foldvarid93/JBC_SolderingStation/01_Version1/02_Software/03_Matlab/untitled.jpg

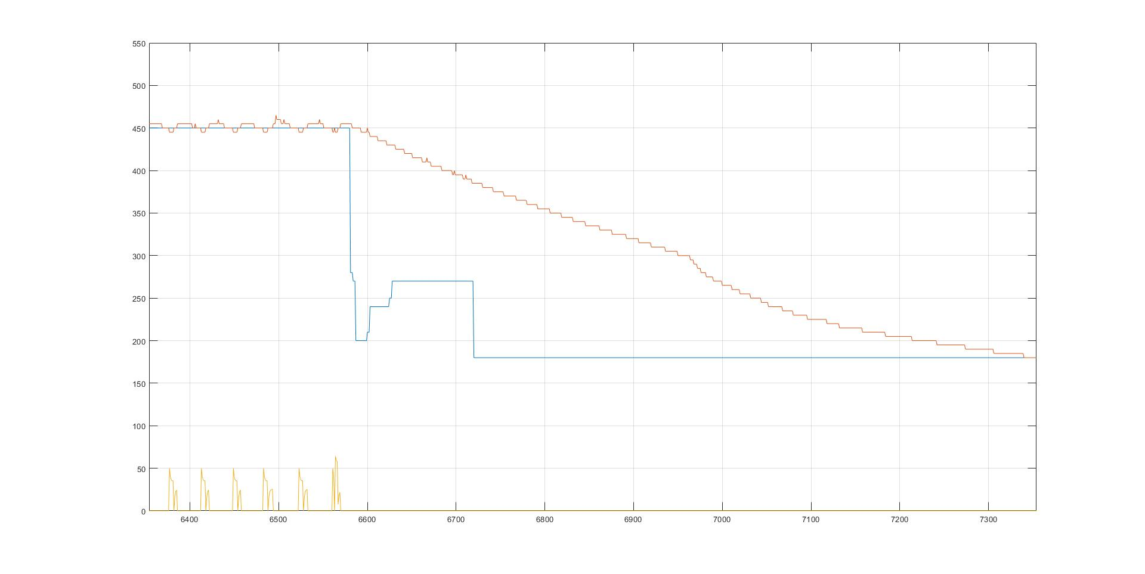
01_Version1/02_Software/03_Matlab/untitled.jpg
