foldvarid93/JBC_SolderingStation/01_Version1/02_Software/03_Matlab/WebinarElement14/3 Temperature Logging/TMP36_DataSheet_Image.JPG

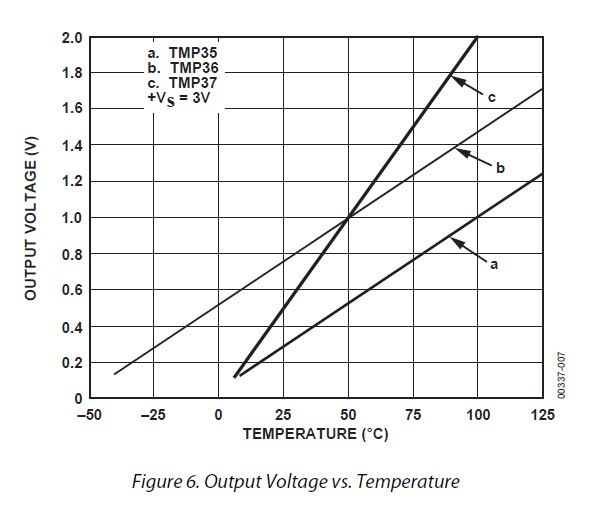
01_Version1/02_Software/03_Matlab/WebinarElement14/3 Temperature Logging/TMP36_DataSheet_Image.JPG
