foldvarid93/JBC_SolderingStation/01_Version1/01_Hardware/02_3D/Assem1.SLDASM

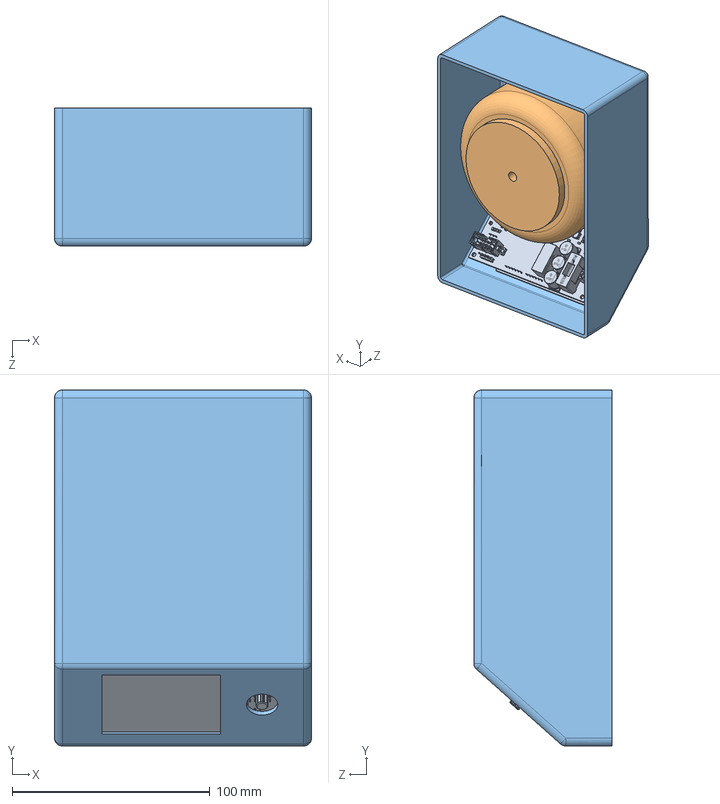
[picture p31: CAD file, 2023-04-08]
01_Version1/01_Hardware/02_3D/Assem1.SLDASM
130.0 x 180.0 x 70.0 mm
JBC_SolderingIron2
Transformer
housing
