foldvarid93/JBC_SolderingStation/01_Version1/01_Hardware/02_3D/JBC_SolderingIron.SLDASM

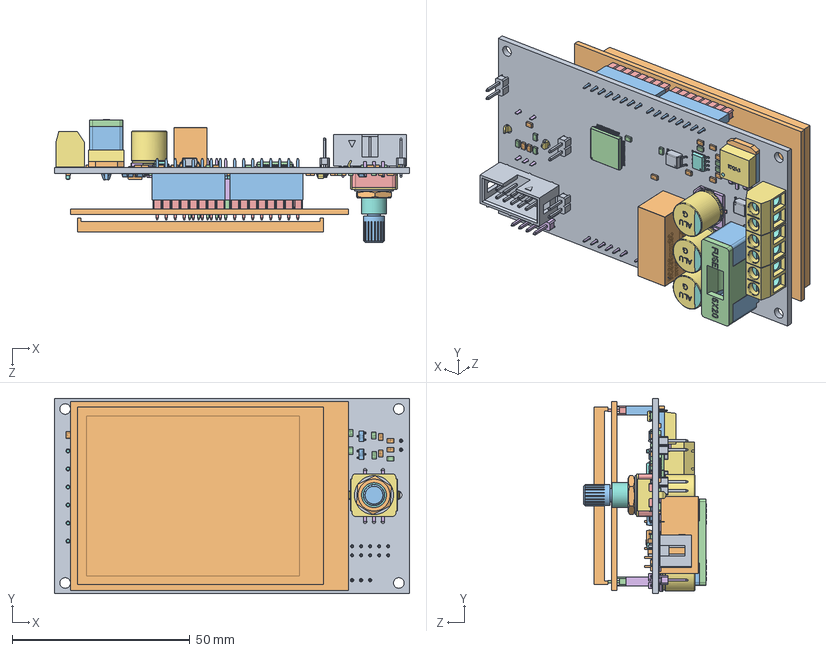
[picture p32: CAD file, 2023-04-08]
01_Version1/01_Hardware/02_3D/JBC_SolderingIron.SLDASM
100.0 x 55.0 x 34.7 mm
0805_Fekete_R x 35
SOT23 x 5
0805_Barna_C x 26
Pins_1 x 3
Fuss_1 x 3
K_X_F6rper_1 x 3
Beschriftung_1 x 3
SIL2 x 3
baseboard
HEADER8 x 2
SIL6 x 2
SIL8 x 2
HEADER6 x 2
User_Library-SOT23-6-2
SO-8 x 2
SO4-170-2.54 x 2
mps_dcdc_ncs3s_sc_a
User_Library-SOT-223-1
User_Library-LQFP64-0_5
SW3dPS-TO263-3S_Board9
SW3dPS-TO263-3S_Extruded14 x 2
SW3dPS-TO263-3S_Extruded11
SW3dPS-TO263-3S_Cylinder1
SW3dPS-TO263-3S_Extruded12
SW3dPS-TO263-3S_Extruded21
SW3dPS-TO263-3S_Extruded16
SW3dPS-TO263-3S_Extruded19
SW3dPS-TO263-3S_Board5 x 2
SW3dPS-TO263-3S_Extruded13 x 2
SW3dPS-TO263-3S_Extruded18
SW3dPS-TO263-3S_Board7
SW3dPS-TO263-3S_Board6
SW3dPS-TO263-3S_Extruded15
SW3dPS-TO263-3S_Extruded17
SW3dPS-TO263-3S_Board8
SW3dPS-TO263-3S_Extruded20
SIL4
User_Library-TB2_TB_case_1 x 3
User_Library-TB2_TB_screw_1 x 6
BH-10_64
1812L
12mm_Incremental_Encoder_Base_1
12mm_Incremental_Encoder_Pin_1 x 5
12mm_Incremental_Encoder_Anti-Rotation_Plate_1
12mm_Incremental_Encoder_Threaded_Tube_1
12mm_Incremental_Encoder_Washer_1
M7x0.75_Hex_Nut_1
12mm_Incremental_Encoder_Shaft
pin x 4
pin(Mirror) x 4
icbody x 4
User_Library-Tantalum_Capacitor_Case_A_Tantalum_case_A_part1 x 2
User_Library-Tantalum_Capacitor_Case_A_Tantalum_case_A_part2 x 4
SOIC-4_(Fairchild)
