foldvarid93/JBC_SolderingStation/01_Version1/01_Hardware/02_3D/v2/RPC1-12RB-6P.SLDPRT

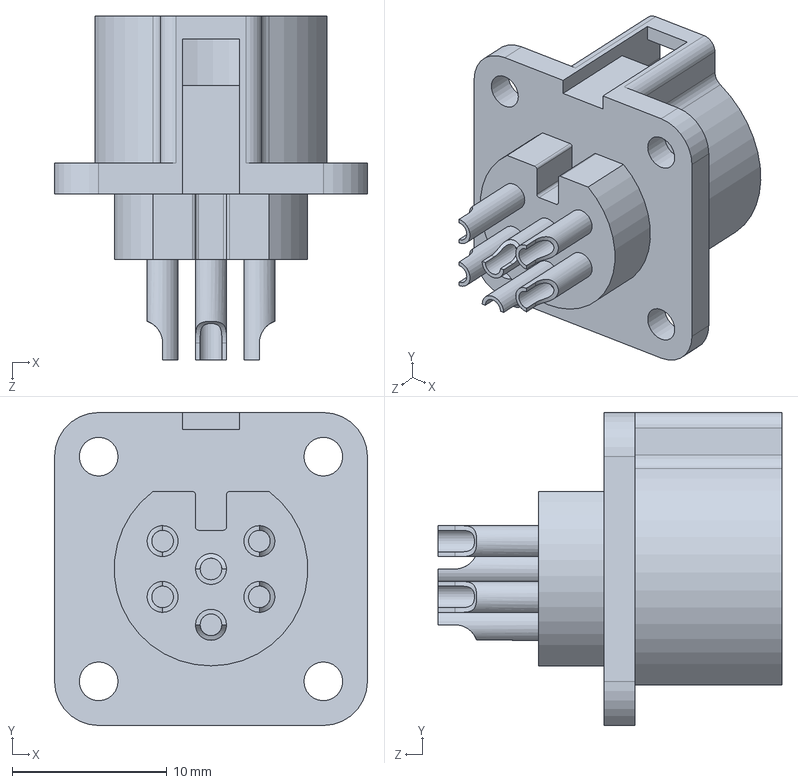
[picture p33: CAD file, 2023-04-08]
01_Version1/01_Hardware/02_3D/v2/RPC1-12RB-6P.SLDPRT
20.2 x 20.2 x 22.2 mm
