foldvarid93/JBC_SolderingStation/01_Version1/01_Hardware/02_3D/v2/PowerConn.SLDPRT

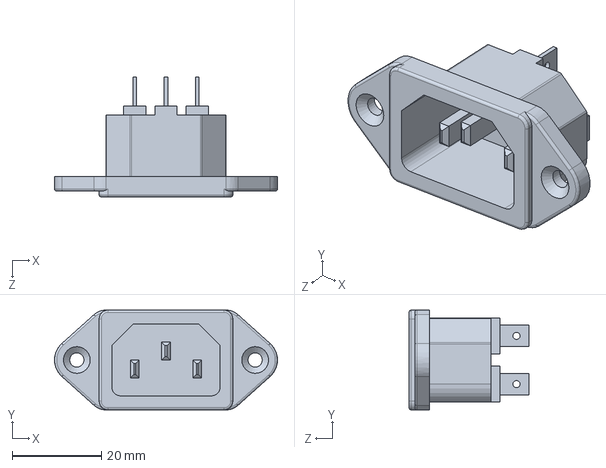
[picture p34: CAD file, 2023-04-08]
01_Version1/01_Hardware/02_3D/v2/PowerConn.SLDPRT
50.0 x 22.4 x 26.9 mm
