foldvarid93/JBC_SolderingStation/01_Version1/01_Hardware/02_3D/v2/haz1.SLDPRT

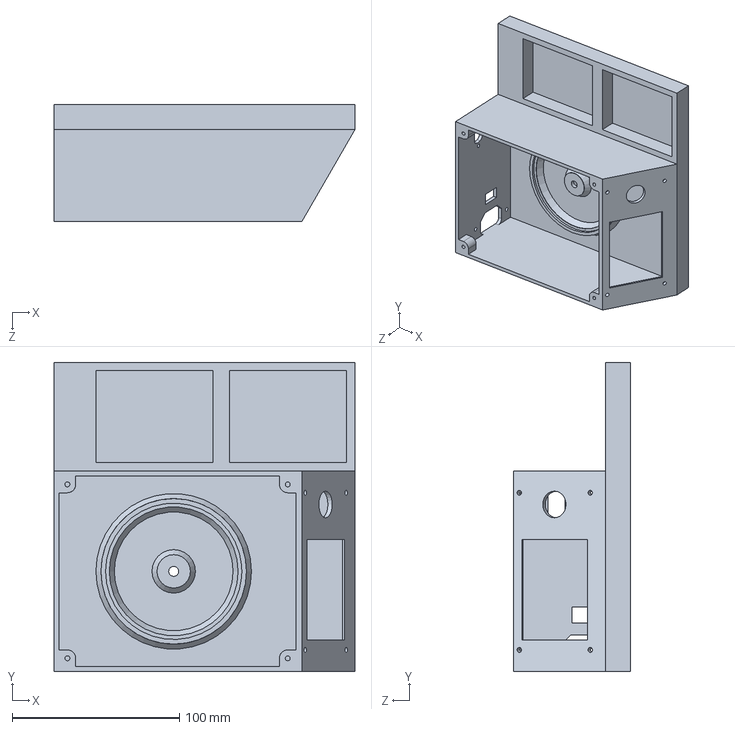
[picture p35: CAD file, 2023-04-08]
01_Version1/01_Hardware/02_3D/v2/haz1.SLDPRT
180.0 x 185.0 x 70.0 mm
