foldvarid93/JBC_SolderingStation/01_Version1/01_Hardware/02_3D/v2/D-Sub_9.STEP

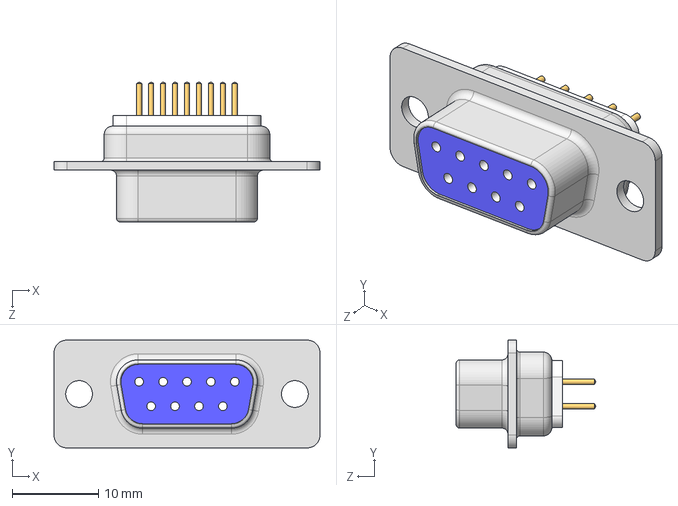
[picture p36: CAD file, 2023-04-08]
01_Version1/01_Hardware/02_3D/v2/D-Sub_9.STEP
30.8 x 12.5 x 16.2 mm
