foldvarid93/JBC_SolderingStation/01_Version1/01_Hardware/02_3D/v2/User Library-KCD11.step

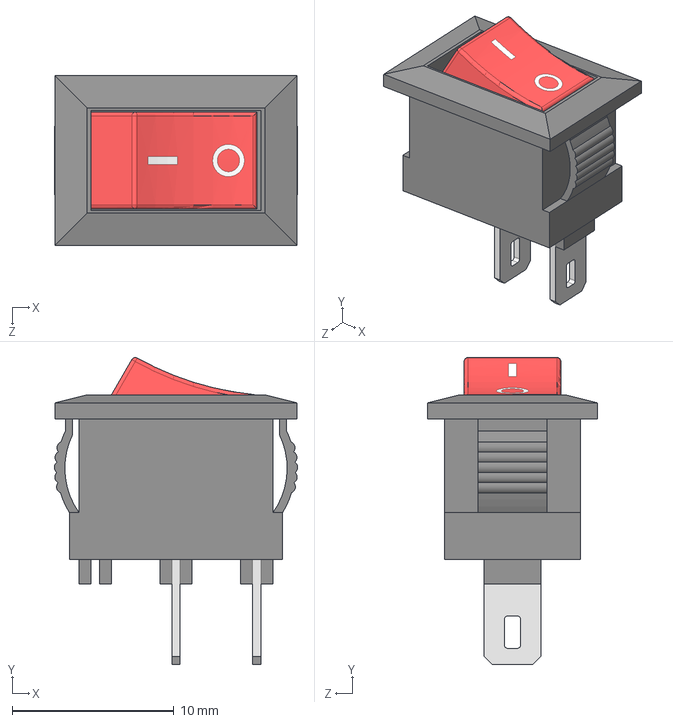
[picture p37: CAD file, 2023-04-08]
01_Version1/01_Hardware/02_3D/v2/User Library-KCD11.step
15.1 x 19.0 x 10.5 mm
