foldvarid93/JBC_SolderingStation/02_Version2/02_Software/01_EmbeddedSw/Application/inc/Application.h

/*
 * Application.h
 *
 *  Created on: Nov 1, 2019
 */

#ifndef APPLICATION_H_
#define APPLICATION_H_
/*includes*/
#include "main.h"
#include "tim.h"
#include "stdlib.h"
#include "string.h"
#include "stdio.h"
#include "math.h"
#include "adc.h"
#include "i2c.h"
#include "tim.h"
#include "usart.h"
#include "gpio.h"
#include "stdbool.h"
#include "eeprom.h"
#include "crc.h"
#include "DIALOG.h"
#include "GUI.h"
#include "portmacro.h"
/*Defines*/
#define NumberOfADCSampleAvegrage (3u)
/*Function declarations*/
void LCD_text(const char *q);
void LCD_write(unsigned char c, unsigned char d);
void LCD_init(void);
void user_pwm_setvalue(uint16_t value);
void ftoa(float n, char *res, int afterpoint);
void SendMeasurements(void);
void MainTask(void);
void MainInit(void);
void StateMachine(void);
extern void StateMachine(void);
void PID_Discrete(void);
void PID_Continous(void);
void InterruptTaskHandler(uint16_t);
void TimerCallback_1ms(void);
#endif /* APPLICATION_H_ */
