foldvarid93/JBC_SolderingStation/02_Version2/02_Software/01_EmbeddedSw/LCD/inc/ILI9341.h

/**
 * @file ILI9341.h
 *
 */

#ifndef ILI9341_H
#define ILI9341_H

#ifdef __cplusplus
extern "C" {
#endif

/*********************
 *      INCLUDES
 *********************/
#include <stdbool.h>
#include "LCDConf.h"
#ifndef LV_DRV_NO_CONF
#ifdef LV_CONF_INCLUDE_SIMPLE
#include "lv_drv_conf.h"
#else
#include "lv_drv_conf.h"
#endif
#endif

#if USE_ILI9341

#ifdef LV_LVGL_H_INCLUDE_SIMPLE
#include "lvgl.h"
#else
#include "../../../lvgl/lvgl.h"
#endif

#if LV_COLOR_DEPTH != 16
#error "ILI9341 currently supports 'LV_COLOR_DEPTH == 16'. Set it in lv_conf.h"
#endif

#if LV_COLOR_16_SWAP != 1
//#error "ILI9341 SPI requires LV_COLOR_16_SWAP == 1. Set it in lv_conf.h"
#endif

/*********************
 *      DEFINES
 *********************/
#define ILI9341_BGR true
#define ILI9341_RGB false

#define ILI9341_CMD_MODE    0
#define ILI9341_DATA_MODE   1

#define ILI9341_TFTWIDTH    240
#define ILI9341_TFTHEIGHT   320

/**********************
 *      TYPEDEFS
 **********************/

/**********************
 * GLOBAL PROTOTYPES
 **********************/
void ili9341_init(void);
void ili9341_flush(lv_disp_drv_t * drv, const lv_area_t * area, lv_color_t * color_p);
void ili9341_rotate(int degrees, bool bgr);
/**********************
 *      MACROS
 **********************/

#endif /* USE_ILI9341 */

#ifdef __cplusplus
} /* extern "C" */
#endif

#endif /* ILI9341_H */
