foldvarid93/JBC_SolderingStation/02_Version2/02_Software/01_EmbeddedSw/GUI/inc/GUIDRV_Lin_Private.h

#define GUIDRV_LIN_PRIVATE_H
#include <string.h>
#if defined(__cplusplus)
extern "C" {
#endif
#if defined(WIN32)
  U16  SIM_Lin_ReadMem16  (unsigned int Off);
  U32  SIM_Lin_ReadMem32  (unsigned int Off);
  U8   SIM_Lin_ReadMem08p (U8  * p);
  U32  SIM_Lin_ReadMem32p (U32 * p);
  void SIM_Lin_WriteMem16 (unsigned int Off, U16 Data);
  void SIM_Lin_WriteMem32 (unsigned int Off, U32 Data);
  void SIM_Lin_WriteMem08p(U8  * p, U8 Data);
  void SIM_Lin_WriteMem16p(U16 * p, U16 Data);
  void SIM_Lin_WriteMem32p(U32 * p, U32 Data);
  void SIM_Lin_memcpy     (void * pDst, const void * pSrc, int Len);
  void SIM_Lin_memset     (void * pDst, U8 Value, U32 Len);
  void SIM_Lin_SetVRAMAddr(int LayerIndex, void * pVRAM);
  void SIM_Lin_SetVRAMSize(int LayerIndex, int vxSize, int vySize, int xSize, int ySize);
  void SIM_Lin_CopyBuffer (int IndexSrc, int IndexDst);
  void SIM_Lin_ShowBuffer (int Index);
  #define LCD_READ_MEM16(VRAMAddr, Off)        SIM_Lin_ReadMem16(Off)
  #define LCD_READ_MEM32(VRAMAddr, Off)        SIM_Lin_ReadMem32(Off)
  #define LCD_READ_MEM08P(p)                   SIM_Lin_ReadMem08p(p)
  #define LCD_READ_MEM32P(p)                   SIM_Lin_ReadMem32p(p)
  #define LCD_WRITE_MEM16(VRAMAddr, Off, Data) SIM_Lin_WriteMem16(Off, Data)
  #define LCD_WRITE_MEM32(VRAMAddr, Off, Data) SIM_Lin_WriteMem32(Off, Data)
  #define LCD_WRITE_MEM08P(p, Data)            SIM_Lin_WriteMem08p(p, Data)
  #define LCD_WRITE_MEM16P(p, Data)            SIM_Lin_WriteMem16p(p, Data)
  #define LCD_WRITE_MEM32P(p, Data)            SIM_Lin_WriteMem32p(p, Data)
  #undef  GUI__MEMCPY
  #define GUI__MEMCPY(pDst, pSrc, Len)         SIM_Lin_memcpy(pDst, pSrc, Len)
  #undef  GUI__MEMSET
  #define GUI__MEMSET(pDst, Value, Len)        SIM_Lin_memset(pDst, Value, Len)
#else
  #define LCD_READ_MEM16(VRAMAddr, Off)        (*((U16 *)VRAMAddr + (U32)Off))
  #define LCD_READ_MEM32(VRAMAddr, Off)        (*((U32 *)VRAMAddr + (U32)Off))
  #define LCD_READ_MEM08P(p)                   (*((U8  *)p))
  #define LCD_READ_MEM32P(p)                   (*((U32 *)p))
  #define LCD_WRITE_MEM16(VRAMAddr, Off, Data) *((U16 *)VRAMAddr + (U32)Off) = (U16)(Data)
  #define LCD_WRITE_MEM32(VRAMAddr, Off, Data) *((U32 *)VRAMAddr + (U32)Off) = Data
  #define LCD_WRITE_MEM08P(p, Data)            *((U8  *)p) = (U8)(Data)
  #define LCD_WRITE_MEM16P(p, Data)            *((U16 *)p) = (U16)(Data)
  #define LCD_WRITE_MEM32P(p, Data)            *((U32 *)p) = Data
#endif
  #define WRITE_MEM16(VRAMAddr, Off, Data) LCD_WRITE_MEM16(VRAMAddr, Off, Data)
  #define WRITE_MEM32(VRAMAddr, Off, Data) LCD_WRITE_MEM32(VRAMAddr, Off, Data)
  #define READ_MEM08P(p)                   LCD_READ_MEM08P(p)
  #define READ_MEM16(VRAMAddr, Off)        LCD_READ_MEM16(VRAMAddr, Off)
  #define READ_MEM32(VRAMAddr, Off)        LCD_READ_MEM32(VRAMAddr, Off)
  #define READ_MEM32P(p)                   LCD_READ_MEM32P(p)
  #define WRITE_MEM08P(p, Data)            LCD_WRITE_MEM08P(p, Data)
  #define WRITE_MEM16P(p, Data)            LCD_WRITE_MEM16P(p, Data)
  #define WRITE_MEM32P(p, Data)            LCD_WRITE_MEM32P(p, Data)
#define OFF2PTR08(VRAMAddr, Off)     (U8  *)((U8 *)VRAMAddr + (Off     ))
#define OFF2PTR16(VRAMAddr, Off)     (U16 *)((U8 *)VRAMAddr + (Off << 1))
#define OFF2PTR32(VRAMAddr, Off)     (U32 *)((U8 *)VRAMAddr + (Off << 2))
#define DRIVER_CONTEXT DRIVER_CONTEXT_LIN
#define DEFAULT_CONTEXT_MEMBERS                               \
  U32 VRAMAddr;                                               \
  U32 BaseAddr;                                               \
  U32 * aBufferPTR;                                           \
  int BufferIndex;                                            \
  int xSize, ySize;                                           \
  int vxSize, vySize;                                         \
  int vxSizePhys;                                             \
  int xPos, yPos;                                             \
  int Alpha;                                                  \
  int IsVisible;                                              \
  void (* pfFillRect)  (int ,                 \
                        int ,                         \
                        int ,                         \
                        int ,                         \
                        int ,                         \
                        U32 );                \
  void (* pfCopyBuffer)(int ,                 \
                        int ,                   \
                        int );                  \
  void (* pfDrawBMP1)  (int ,                 \
                        int ,                          \
                        int ,                          \
                        U8 const * ,                   \
                        int ,                       \
                        int ,                      \
                        int ,                      \
                        int ,               \
                        const LCD_PIXELINDEX * ); \
  void (* pfDrawBMP8)  (int ,                 \
                        int ,                          \
                        int ,                          \
                        U8 const * ,                   \
                        int ,                      \
                        int ,                      \
                        int ,               \
                        const LCD_PIXELINDEX * ); \
  void (* pfCopyRect)  (int ,                 \
                        int ,                         \
                        int ,                         \
                        int ,                         \
                        int ,                         \
                        int ,                      \
                        int );                     \
  void (* pfSetPos)    (int ,                 \
                        int ,                       \
                        int );
  #define PRIVATE_CONTEXT_MEMBERS
#define DEFAULT_MANAGEMENT_GETDEVFUNC()                                             \
  case LCD_DEVFUNC_SET_VRAM_ADDR:                                                   \
    return (void (*)(void))_SetVRAMAddr;                                            \
  case LCD_DEVFUNC_SET_BUFFERPTR:                                                   \
    return (void (*)(void))_SetVRAM_BufferPTR;                                      \
  case LCD_DEVFUNC_SET_VSIZE:                                                       \
    return (void (*)(void))_SetVSize;                                               \
  case LCD_DEVFUNC_SET_SIZE:                                                        \
    return (void (*)(void))_SetSize;                                                \
  case LCD_DEVFUNC_SETPOS:                                                          \
    return (void (*)(void))_SetPos;                                                 \
  case LCD_DEVFUNC_GETPOS:                                                          \
    return (void (*)(void))_GetPos;                                                 \
  case LCD_DEVFUNC_SETALPHA:                                                        \
    return (void (*)(void))_SetAlpha;                                               \
  case LCD_DEVFUNC_SETVIS:                                                          \
    return (void (*)(void))_SetVis;                                                 \
  case LCD_DEVFUNC_INIT:                                                            \
    return (void (*)(void))_Init;                                                   \
  case LCD_DEVFUNC_ON:                                                              \
    return (void (*)(void))_On;                                                     \
  case LCD_DEVFUNC_OFF:                                                             \
    return (void (*)(void))_Off;                                                    \
  case LCD_DEVFUNC_ALPHAMODE:                                                       \
    return (void (*)(void))_SetAlphaMode;                                           \
  case LCD_DEVFUNC_CHROMAMODE:                                                      \
    return (void (*)(void))_SetChromaMode;                                          \
  case LCD_DEVFUNC_CHROMA:                                                          \
    return (void (*)(void))_SetChroma;                                              \
  case LCD_DEVFUNC_COPYBUFFER:                                                      \
    return (void (*)(void))_CopyBuffer;                                             \
  case LCD_DEVFUNC_SHOWBUFFER:                                                      \
    return (void (*)(void))_ShowBuffer;                                             \
  case LCD_DEVFUNC_SETFUNC:                                                         \
    return (void (*)(void))_SetDevFunc;                                             \
  case LCD_DEVFUNC_FILLRECT:                                                        \
    return (void (*)(void))((DRIVER_CONTEXT *)(*ppDevice)->u.pContext)->pfFillRect; \
  case LCD_DEVFUNC_DRAWBMP_1BPP:                                                    \
    return (void (*)(void))((DRIVER_CONTEXT *)(*ppDevice)->u.pContext)->pfDrawBMP1; \
  case LCD_DEVFUNC_DRAWBMP_8BPP:                                                    \
    return (void (*)(void))((DRIVER_CONTEXT *)(*ppDevice)->u.pContext)->pfDrawBMP8; \
  case LCD_DEVFUNC_COPYRECT:                                                        \
    return (void (*)(void))((DRIVER_CONTEXT *)(*ppDevice)->u.pContext)->pfCopyRect;
  #define PRIVATE_MANAGEMENT_GETDEVFUNC()
#define DEFAULT_MANAGEMENT_SETDEVFUNC()                                                                                                                                      \
    case LCD_DEVFUNC_FILLRECT:                                                                                                                                               \
      pContext->pfFillRect   = (void (*)(int LayerIndex, int x0, int y0, int x1, int y1, U32 PixelIndex))pFunc;                                                              \
      break;                                                                                                                                                                 \
    case LCD_DEVFUNC_COPYBUFFER:                                                                                                                                             \
      pContext->pfCopyBuffer = (void (*)(int LayerIndex, int IndexSrc, int IndexDst))pFunc;                                                                                  \
      break;                                                                                                                                                                 \
    case LCD_DEVFUNC_DRAWBMP_1BPP:                                                                                                                                           \
      pContext->pfDrawBMP1   = (void (*)(int LayerIndex, int x, int y, U8 const * p, int Diff, int xSize, int ySize, int BytesPerLine, const LCD_PIXELINDEX * pTrans))pFunc; \
      break;                                                                                                                                                                 \
    case LCD_DEVFUNC_DRAWBMP_8BPP:                                                                                                                                           \
      pContext->pfDrawBMP8   = (void (*)(int LayerIndex, int x, int y, U8 const * p, int xSize, int ySize, int BytesPerLine, const LCD_PIXELINDEX * pTrans))pFunc;           \
      break;                                                                                                                                                                 \
    case LCD_DEVFUNC_COPYRECT:                                                                                                                                               \
      pContext->pfCopyRect   = (void (*)(int LayerIndex, int x0, int y0, int x1, int y1, int xSize, int ySize))pFunc;                                                        \
      break;                                                                                                                                                                 \
    case LCD_DEVFUNC_SETPOS:                                                                                                                                                 \
      pContext->pfSetPos     = (void (*)(int LayerIndex, int xPos, int yPos))pFunc;                                                                                          \
      break;
  #define PRIVATE_MANAGEMENT_SETDEVFUNC()
  #define LCD_MIRROR 0
#if (LCD_MIRROR == 2)
#define MIRROR(x) x = ((x & 0x000000ffUL) <<  8) \
                    | ((x & 0x0000ff00UL) >>  8) \
                    | ((x & 0x00ff0000UL) <<  8) \
                    | ((x & 0xff000000UL) >>  8)
#else
#define MIRROR(x) x = ((x & 0x000000ffUL) << 24) \
                    | ((x & 0x0000ff00UL) <<  8) \
                    | ((x & 0x00ff0000UL) >>  8) \
                    | ((x & 0xff000000UL) >> 24)
#endif
typedef struct {
  DEFAULT_CONTEXT_MEMBERS
  PRIVATE_CONTEXT_MEMBERS
} DRIVER_CONTEXT;
static int _InitOnce(GUI_DEVICE * pDevice) {
  if (pDevice->u.pContext == NULL) {
    pDevice->u.pContext = GUI_ALLOC_GetFixedBlock(sizeof(DRIVER_CONTEXT));
    GUI__memset((U8 *)pDevice->u.pContext, 0, sizeof(DRIVER_CONTEXT));
  }
  return pDevice->u.pContext ? 0 : 1;
}
static void _GetRect(GUI_DEVICE * pDevice, LCD_RECT * pRect) {
  DRIVER_CONTEXT * pContext;
  pContext = (DRIVER_CONTEXT *)pDevice->u.pContext;
  pRect->x0 = 0;
  pRect->y0 = 0;
  pRect->x1 = pContext->vxSize - 1;
  pRect->y1 = pContext->vySize - 1;
}
static void _SetVis(GUI_DEVICE * pDevice, int OnOff) {
  DRIVER_CONTEXT * pContext;
  LCD_X_SETVIS_INFO Data = {0};
  _InitOnce(pDevice);
  if (pDevice->u.pContext) {
    pContext = (DRIVER_CONTEXT *)pDevice->u.pContext;
    pContext->IsVisible = OnOff;
    Data.OnOff = OnOff;
    LCD_X_DisplayDriver(pDevice->LayerIndex, LCD_X_SETVIS, (void *)&Data);
  }
}
static void _SetPos(GUI_DEVICE * pDevice, int xPos, int yPos) {
  DRIVER_CONTEXT * pContext;
  int xSizeDisplay, ySizeDisplay, xSizeLayer, ySizeLayer, BitsPerPixel;
  LCD_X_SETPOS_INFO PosInfo = {0};
  _InitOnce(pDevice);
  if (pDevice->u.pContext) {
    pContext = (DRIVER_CONTEXT *)pDevice->u.pContext;
    if (pContext->pfSetPos) {
      pContext->pfSetPos(pDevice->LayerIndex, xPos, yPos);
    } else {
      pContext->xPos = xPos;
      pContext->yPos = yPos;
      xSizeDisplay  = LCD_GetXSizeDisplay();
      ySizeDisplay  = LCD_GetYSizeDisplay();
      xSizeLayer    = pContext->xSize;
      ySizeLayer    = pContext->ySize;
      BitsPerPixel  = pDevice->pDeviceAPI->pfGetDevProp(pDevice, LCD_DEVCAP_BITSPERPIXEL);
      PosInfo.BytesPerPixel = (BitsPerPixel + 7) / 8;
      if (xPos < 0) {
        PosInfo.Off -= xPos * PosInfo.BytesPerPixel;
        PosInfo.xPos = 0;
        PosInfo.xLen = xSizeLayer + xPos;
      } else {
        PosInfo.xPos = xPos;
        PosInfo.xLen = xSizeLayer;
        if ((PosInfo.xPos + PosInfo.xLen) > xSizeDisplay) {
          PosInfo.xLen = xSizeDisplay - xPos;
        }
      }
      if (yPos < 0) {
        PosInfo.Off -= yPos * PosInfo.BytesPerPixel * xSizeLayer;
        PosInfo.yPos = 0;
        PosInfo.yLen = ySizeLayer + yPos;
      } else {
        PosInfo.yPos = yPos;
        PosInfo.yLen = ySizeLayer;
        if ((PosInfo.yPos + PosInfo.yLen) > ySizeDisplay) {
          PosInfo.yLen = ySizeDisplay - yPos;
        }
      }
      if ((PosInfo.xLen <= 0) || (PosInfo.yLen <= 0) || (PosInfo.xPos >= xSizeDisplay) || (PosInfo.yPos >= ySizeDisplay)) {
        if (pContext->IsVisible == 1) {
          _SetVis(pDevice, 0);
        }
        return;
      }
      if (pContext->IsVisible == 0) {
        _SetVis(pDevice, 1);
      }
      LCD_X_DisplayDriver(pDevice->LayerIndex, LCD_X_SETPOS, (void *)&PosInfo);
    }
  }
}
static void _GetPos(GUI_DEVICE * pDevice, int * pxPos, int * pyPos) {
  DRIVER_CONTEXT * pContext;
  _InitOnce(pDevice);
  if (pDevice->u.pContext) {
    pContext = (DRIVER_CONTEXT *)pDevice->u.pContext;
    *pxPos = pContext->xPos;
    *pyPos = pContext->yPos;
  }
}
static void _SetAlpha(GUI_DEVICE * pDevice, int Alpha) {
  DRIVER_CONTEXT * pContext;
  LCD_X_SETALPHA_INFO Data = {0};
  _InitOnce(pDevice);
  if (pDevice->u.pContext) {
    pContext = (DRIVER_CONTEXT *)pDevice->u.pContext;
    pContext->Alpha = Alpha;
    Data.Alpha = Alpha;
    LCD_X_DisplayDriver(pDevice->LayerIndex, LCD_X_SETALPHA, (void *)&Data);
  }
}
static int  _Init(GUI_DEVICE * pDevice) {
  int r;
  r = _InitOnce(pDevice);
  r |= LCD_X_DisplayDriver(pDevice->LayerIndex, LCD_X_INITCONTROLLER, NULL);
  return r;
}
static void _On (GUI_DEVICE * pDevice) {
  LCD_X_DisplayDriver(pDevice->LayerIndex, LCD_X_ON, NULL);
}
static void _Off (GUI_DEVICE * pDevice) {
  LCD_X_DisplayDriver(pDevice->LayerIndex, LCD_X_OFF, NULL);
}
static void _SetAlphaMode(GUI_DEVICE * pDevice, int AlphaMode) {
  LCD_X_SETALPHAMODE_INFO Data = {0};
  Data.AlphaMode = AlphaMode;
  LCD_X_DisplayDriver(pDevice->LayerIndex, LCD_X_SETALPHAMODE, (void *)&Data);
}
static void _SetChromaMode(GUI_DEVICE * pDevice, int ChromaMode) {
  LCD_X_SETCHROMAMODE_INFO Data = {0};
  Data.ChromaMode = ChromaMode;
  LCD_X_DisplayDriver(pDevice->LayerIndex, LCD_X_SETCHROMAMODE, (void *)&Data);
}
static void _SetChroma(GUI_DEVICE * pDevice, LCD_COLOR ChromaMin, LCD_COLOR ChromaMax) {
  LCD_X_SETCHROMA_INFO Data = {0};
  Data.ChromaMin = ChromaMin;
  Data.ChromaMax = ChromaMax;
  LCD_X_DisplayDriver(pDevice->LayerIndex, LCD_X_SETCHROMA, (void *)&Data);
}
static void _CopyBuffer(GUI_DEVICE * pDevice, int IndexSrc, int IndexDst) {
  DRIVER_CONTEXT * pContext;
  #if (!defined(WIN32))
    U32 AddrSrc, AddrDst;
    I32 BufferSize;
    int BitsPerPixel;
  #endif
  _InitOnce(pDevice);
  if (pDevice->u.pContext) {
    pContext = (DRIVER_CONTEXT *)pDevice->u.pContext;
    if (IndexSrc != IndexDst) {
      #if defined(WIN32)
        SIM_Lin_CopyBuffer(IndexSrc, IndexDst);
      #else
        BitsPerPixel = pDevice->pDeviceAPI->pfGetDevProp(pDevice, LCD_DEVCAP_BITSPERPIXEL);
        BufferSize = (((U32)pContext->vxSize * pContext->ySize * BitsPerPixel) >> 3);
        if (pContext->aBufferPTR) {
          AddrSrc = *(pContext->aBufferPTR + IndexSrc);
          AddrDst = *(pContext->aBufferPTR + IndexDst);
        } else {
          AddrSrc = pContext->BaseAddr + BufferSize * IndexSrc;
          AddrDst = pContext->BaseAddr + BufferSize * IndexDst;
        }
        if (pContext->pfCopyBuffer) {
          pContext->pfCopyBuffer(pDevice->LayerIndex, IndexSrc, IndexDst);
        } else {
          GUI__MEMCPY((void *)AddrDst, (void *)AddrSrc, BufferSize);
        }
        pContext->VRAMAddr = AddrDst;
      #endif
    }
  }
}
static void _ShowBuffer(GUI_DEVICE * pDevice, int Index) {
  LCD_X_SHOWBUFFER_INFO Data = {0};
  _InitOnce(pDevice);
  if (pDevice->u.pContext) {
    #if defined(WIN32)
      SIM_Lin_ShowBuffer(Index);
    #else
      Data.Index = Index;
      LCD_X_DisplayDriver(pDevice->LayerIndex, LCD_X_SHOWBUFFER, (void *)&Data);
    #endif
  }
}
static void _SetOrg(GUI_DEVICE * pDevice, int x, int y) {
  #if (!defined(WIN32))
    DRIVER_CONTEXT * pContext;
    int Orientation;
  #endif
  LCD_X_SETORG_INFO Data = {0};
  #if defined(WIN32)
    LCDSIM_SetOrg(x, y, pDevice->LayerIndex);
  #else
    pContext = (DRIVER_CONTEXT *)pDevice->u.pContext;
    Orientation  = LCD_GetMirrorXEx(pDevice->LayerIndex) * GUI_MIRROR_X;
    Orientation |= LCD_GetMirrorYEx(pDevice->LayerIndex) * GUI_MIRROR_Y;
    Orientation |= LCD_GetSwapXYEx (pDevice->LayerIndex) * GUI_SWAP_XY;
    switch (Orientation) {
    case 0:
      Data.xPos = x;
      Data.yPos = y;
      break;
    case GUI_MIRROR_X:
      Data.xPos = pContext->vxSize - pContext->xSize - x;
      Data.yPos = y;
      break;
    case GUI_MIRROR_Y:
      Data.xPos = x;
      Data.yPos = pContext->vySize - pContext->ySize - y;
      break;
    case GUI_MIRROR_X | GUI_MIRROR_Y:
      Data.xPos = pContext->vxSize - pContext->xSize - x;
      Data.yPos = pContext->vySize - pContext->ySize - y;
      break;
    case GUI_SWAP_XY:
      Data.xPos = y;
      Data.yPos = x;
      break;
    case GUI_SWAP_XY | GUI_MIRROR_X:
      Data.xPos = pContext->vySize - pContext->ySize  - y;
      Data.yPos = x;
      break;
    case GUI_SWAP_XY | GUI_MIRROR_Y:
      Data.xPos = y;
      Data.yPos = pContext->vxSize - pContext->xSize  - x;
      break;
    case GUI_SWAP_XY | GUI_MIRROR_X | GUI_MIRROR_Y:
      Data.xPos = pContext->vySize - pContext->ySize  - y;
      Data.yPos = pContext->vxSize - pContext->xSize  - x;
      break;
    }
    LCD_X_DisplayDriver(pDevice->LayerIndex, LCD_X_SETORG, (void *)&Data);
  #endif
}
static void _SetVRAMAddr(GUI_DEVICE * pDevice, void * pVRAM) {
  DRIVER_CONTEXT * pContext;
  LCD_X_SETVRAMADDR_INFO Data = {0};
  _InitOnce(pDevice);
  if (pDevice->u.pContext) {
    pContext = (DRIVER_CONTEXT *)pDevice->u.pContext;
    pContext->VRAMAddr = pContext->BaseAddr = (U32)pVRAM;
    Data.pVRAM = pVRAM;
    LCD_X_DisplayDriver(pDevice->LayerIndex, LCD_X_SETVRAMADDR, (void *)&Data);
  }
  #if defined(WIN32)
    SIM_Lin_SetVRAMAddr(pDevice->LayerIndex, pVRAM);
  #endif
}
static void _SetVRAM_BufferPTR(GUI_DEVICE * pDevice, U32 * pBufferPTR) {
  DRIVER_CONTEXT * pContext;
  _InitOnce(pDevice);
  if (pDevice->u.pContext) {
    pContext = (DRIVER_CONTEXT *)pDevice->u.pContext;
    pContext->aBufferPTR = pBufferPTR;
    pContext->VRAMAddr = *(pBufferPTR + 0);
  }
}
static void _SetVSize(GUI_DEVICE * pDevice, int xSize, int ySize) {
  DRIVER_CONTEXT * pContext;
  #if defined(WIN32)
    int NumBuffers;
  #endif
  _InitOnce(pDevice);
  if (pDevice->u.pContext) {
    #if defined(WIN32)
      NumBuffers = GUI_MULTIBUF_GetNumBuffers();
    #endif
    pContext = (DRIVER_CONTEXT *)pDevice->u.pContext;
    if (LCD_GetSwapXYEx(pDevice->LayerIndex)) {
      #if defined(WIN32)
        pContext->vxSize = xSize * NumBuffers;
      #else
        pContext->vxSize = xSize;
      #endif
      pContext->vySize = ySize;
      pContext->vxSizePhys = ySize;
    } else {
      pContext->vxSize = xSize;
      #if defined(WIN32)
        pContext->vySize = ySize * NumBuffers;
      #else
        pContext->vySize = ySize;
      #endif
      pContext->vxSizePhys = xSize;
    }
  }
  #if defined(WIN32)
    SIM_Lin_SetVRAMSize(pDevice->LayerIndex, pContext->vxSize, pContext->vySize, pContext->xSize, pContext->ySize);
  #endif
}
static void _SetSize(GUI_DEVICE * pDevice, int xSize, int ySize) {
  DRIVER_CONTEXT * pContext;
  LCD_X_SETSIZE_INFO Data = {0};
  _InitOnce(pDevice);
  if (pDevice->u.pContext) {
    pContext = (DRIVER_CONTEXT *)pDevice->u.pContext;
    if (pContext->vxSizePhys == 0) {
      if (LCD_GetSwapXYEx(pDevice->LayerIndex)) {
        pContext->vxSizePhys = ySize;
      } else {
        pContext->vxSizePhys = xSize;
      }
    }
    pContext->xSize = xSize;
    pContext->ySize = ySize;
    Data.xSize = xSize;
    Data.ySize = ySize;
    LCD_X_DisplayDriver(pDevice->LayerIndex, LCD_X_SETSIZE, (void *)&Data);
  }
}
#if defined(__cplusplus)
}
#endif
