foldvarid93/JBC_SolderingStation/02_Version2/02_Software/01_EmbeddedSw/GUI/inc/LISTWHEEL.h

/*********************************************************************
*                SEGGER Microcontroller GmbH & Co. KG                *
*        Solutions for real time microcontroller applications        *
**********************************************************************
*                                                                    *
*        (c) 1996 - 2017  SEGGER Microcontroller GmbH & Co. KG       *
*                                                                    *
*        Internet: www.segger.com    Support:  support@segger.com    *
*                                                                    *
**********************************************************************

** emWin V5.44 - Graphical user interface for embedded applications **
All  Intellectual Property rights  in the Software belongs to  SEGGER.
emWin is protected by  international copyright laws.  Knowledge of the
source code may not be used to write a similar product.  This file may
only be used in accordance with the following terms:

The  software has  been licensed  to STMicroelectronics International
N.V. a Dutch company with a Swiss branch and its headquarters in Plan-
les-Ouates, Geneva, 39 Chemin du Champ des Filles, Switzerland for the
purposes of creating libraries for ARM Cortex-M-based 32-bit microcon_
troller products commercialized by Licensee only, sublicensed and dis_
tributed under the terms and conditions of the End User License Agree_
ment supplied by STMicroelectronics International N.V.
Full source code is available at: www.segger.com

We appreciate your understanding and fairness.
----------------------------------------------------------------------

  ******************************************************************************
  * @attention
  *
  * <h2><center>&copy; Copyright (c) 2018 STMicroelectronics. 
  * All rights reserved.</center></h2>
  *
  * This software component is licensed by ST under Ultimate Liberty license SLA0044,
  * the "License"; You may not use this file except in compliance with the License.
  * You may obtain a copy of the License at:
  *                      http://www.st.com/SLA0044
  *
  ******************************************************************************
----------------------------------------------------------------------
File        : LISTWHEEL.h
Purpose     : LISTWHEEL widget include
--------------------END-OF-HEADER-------------------------------------
*/

#ifndef LISTWHEEL_H
#define LISTWHEEL_H

#include "WM.h"
#include "DIALOG_Intern.h"
#include "WIDGET.h"

#if GUI_WINSUPPORT

#if defined(__cplusplus)
  extern "C" {        // Make sure we have C-declarations in C++ programs
#endif

/*********************************************************************
*
*       Defines
*
**********************************************************************
*/
#define LISTWHEEL_CI_UNSEL 0
#define LISTWHEEL_CI_SEL   1

/*********************************************************************
*
*       Types
*
**********************************************************************
*/
typedef WM_HMEM LISTWHEEL_Handle;

/*********************************************************************
*
*       Standard member functions
*
**********************************************************************
*/
/*********************************************************************
*
*       Create functions
*
**********************************************************************
*/
LISTWHEEL_Handle LISTWHEEL_Create        (const GUI_ConstString * ppText, int x0, int y0, int xSize, int ySize, int Flags);
LISTWHEEL_Handle LISTWHEEL_CreateAsChild (const GUI_ConstString * ppText, WM_HWIN hWinParent, int x0, int y0, int xSize, int ySize, int Flags);
LISTWHEEL_Handle LISTWHEEL_CreateIndirect(const GUI_WIDGET_CREATE_INFO * pCreateInfo, WM_HWIN hWinParent, int x0, int y0, WM_CALLBACK * cb);
LISTWHEEL_Handle LISTWHEEL_CreateEx      (int x0, int y0, int xSize, int ySize, WM_HWIN hParent,
                                          int WinFlags, int ExFlags, int Id, const GUI_ConstString * ppText);
LISTWHEEL_Handle LISTWHEEL_CreateUser    (int x0, int y0, int xSize, int ySize, WM_HWIN hParent,
                                          int WinFlags, int ExFlags, int Id, const GUI_ConstString * ppText, int NumExtraBytes);

/*********************************************************************
*
*       The callback ...
*
* Do not call it directly ! It is only to be used from within an
* overwritten callback.
*/
void LISTWHEEL_Callback(WM_MESSAGE * pMsg);

/*********************************************************************
*
*       Member functions
*
**********************************************************************
*/
void      LISTWHEEL_AddString      (LISTWHEEL_Handle hObj, const char * s);
GUI_COLOR LISTWHEEL_GetBkColor     (LISTWHEEL_Handle hObj, unsigned int Index);
void *    LISTWHEEL_GetItemData    (LISTWHEEL_Handle hObj, unsigned Index); /* not to be documented */
void      LISTWHEEL_GetItemText    (LISTWHEEL_Handle hObj, unsigned Index, char * pBuffer, int MaxSize);
int       LISTWHEEL_GetItemFromPos (LISTWHEEL_Handle hObj, int yPos);
int       LISTWHEEL_GetLBorder     (LISTWHEEL_Handle hObj);
unsigned  LISTWHEEL_GetLineHeight  (LISTWHEEL_Handle hObj);
int       LISTWHEEL_GetNumItems    (LISTWHEEL_Handle hObj);
int       LISTWHEEL_GetPos         (LISTWHEEL_Handle hObj);
int       LISTWHEEL_GetRBorder     (LISTWHEEL_Handle hObj);
int       LISTWHEEL_GetSel         (LISTWHEEL_Handle hObj);
int       LISTWHEEL_GetSnapPosition(LISTWHEEL_Handle hObj);
int       LISTWHEEL_GetTextAlign   (LISTWHEEL_Handle hObj);
GUI_COLOR LISTWHEEL_GetTextColor   (LISTWHEEL_Handle hObj, unsigned int Index);
int       LISTWHEEL_GetUserData    (LISTWHEEL_Handle hObj, void * pDest, int NumBytes);
int       LISTWHEEL_IsMoving       (LISTWHEEL_Handle hObj);
void      LISTWHEEL_MoveToPos      (LISTWHEEL_Handle hObj, unsigned int Index);
int       LISTWHEEL_OwnerDraw      (const WIDGET_ITEM_DRAW_INFO * pDrawItemInfo);
void      LISTWHEEL_SetBkColor     (LISTWHEEL_Handle hObj, unsigned int Index, GUI_COLOR Color);
void      LISTWHEEL_SetDeceleration(LISTWHEEL_Handle hObj, unsigned Deceleration);
void      LISTWHEEL_SetFont        (LISTWHEEL_Handle hObj, const GUI_FONT * pFont);
void      LISTWHEEL_SetItemData    (LISTWHEEL_Handle hObj, unsigned Index, void * pData); /* not to be documented */
void      LISTWHEEL_SetLBorder     (LISTWHEEL_Handle hObj, unsigned BorderSize);
void      LISTWHEEL_SetLineHeight  (LISTWHEEL_Handle hObj, unsigned LineHeight);
void      LISTWHEEL_SetOwnerDraw   (LISTWHEEL_Handle hObj, WIDGET_DRAW_ITEM_FUNC * pfOwnerDraw);
void      LISTWHEEL_SetPos         (LISTWHEEL_Handle hObj, unsigned int Index);
void      LISTWHEEL_SetRBorder     (LISTWHEEL_Handle hObj, unsigned BorderSize);
void      LISTWHEEL_SetSel         (LISTWHEEL_Handle hObj, int Sel);
void      LISTWHEEL_SetSnapPosition(LISTWHEEL_Handle hObj, int SnapPosition);
void      LISTWHEEL_SetText        (LISTWHEEL_Handle hObj, const GUI_ConstString * ppText);
void      LISTWHEEL_SetTextAlign   (LISTWHEEL_Handle hObj, int Align);
void      LISTWHEEL_SetTextColor   (LISTWHEEL_Handle hObj, unsigned int Index, GUI_COLOR Color);
void      LISTWHEEL_SetTimerPeriod (LISTWHEEL_Handle hObj, GUI_TIMER_TIME TimerPeriod);
int       LISTWHEEL_SetUserData    (LISTWHEEL_Handle hObj, const void * pSrc, int NumBytes);
void      LISTWHEEL_SetVelocity    (LISTWHEEL_Handle hObj, int Velocity);

const GUI_FONT * LISTWHEEL_GetFont(LISTWHEEL_Handle hObj);

#if defined(__cplusplus)
  }
#endif

#endif  // GUI_WINSUPPORT
#endif  // LISTWHEEL_H

/*************************** End of file ****************************/
